ozkan/Cockpit-Keyboard/images/CockpitKeyboard.jpg

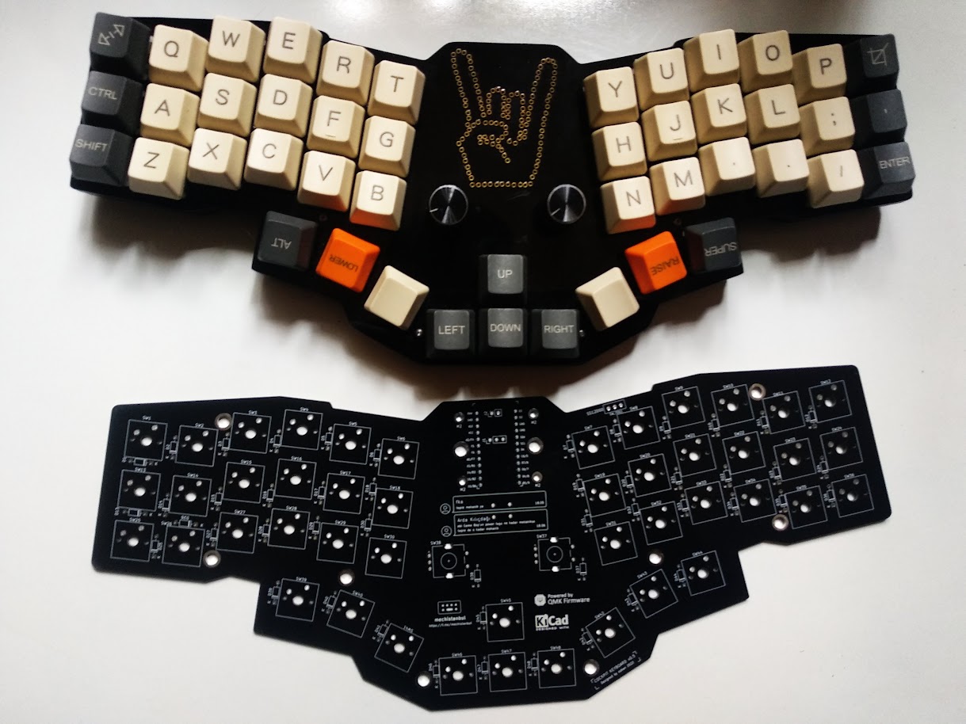
images/CockpitKeyboard.jpg
