ozkan/Cockpit-Keyboard/cockpit_hotswap/pcb/Cockpit.kicad_sch

## KiCad design cockpit_hotswap/pcb/Cockpit.kicad_sch (2024-03-19)

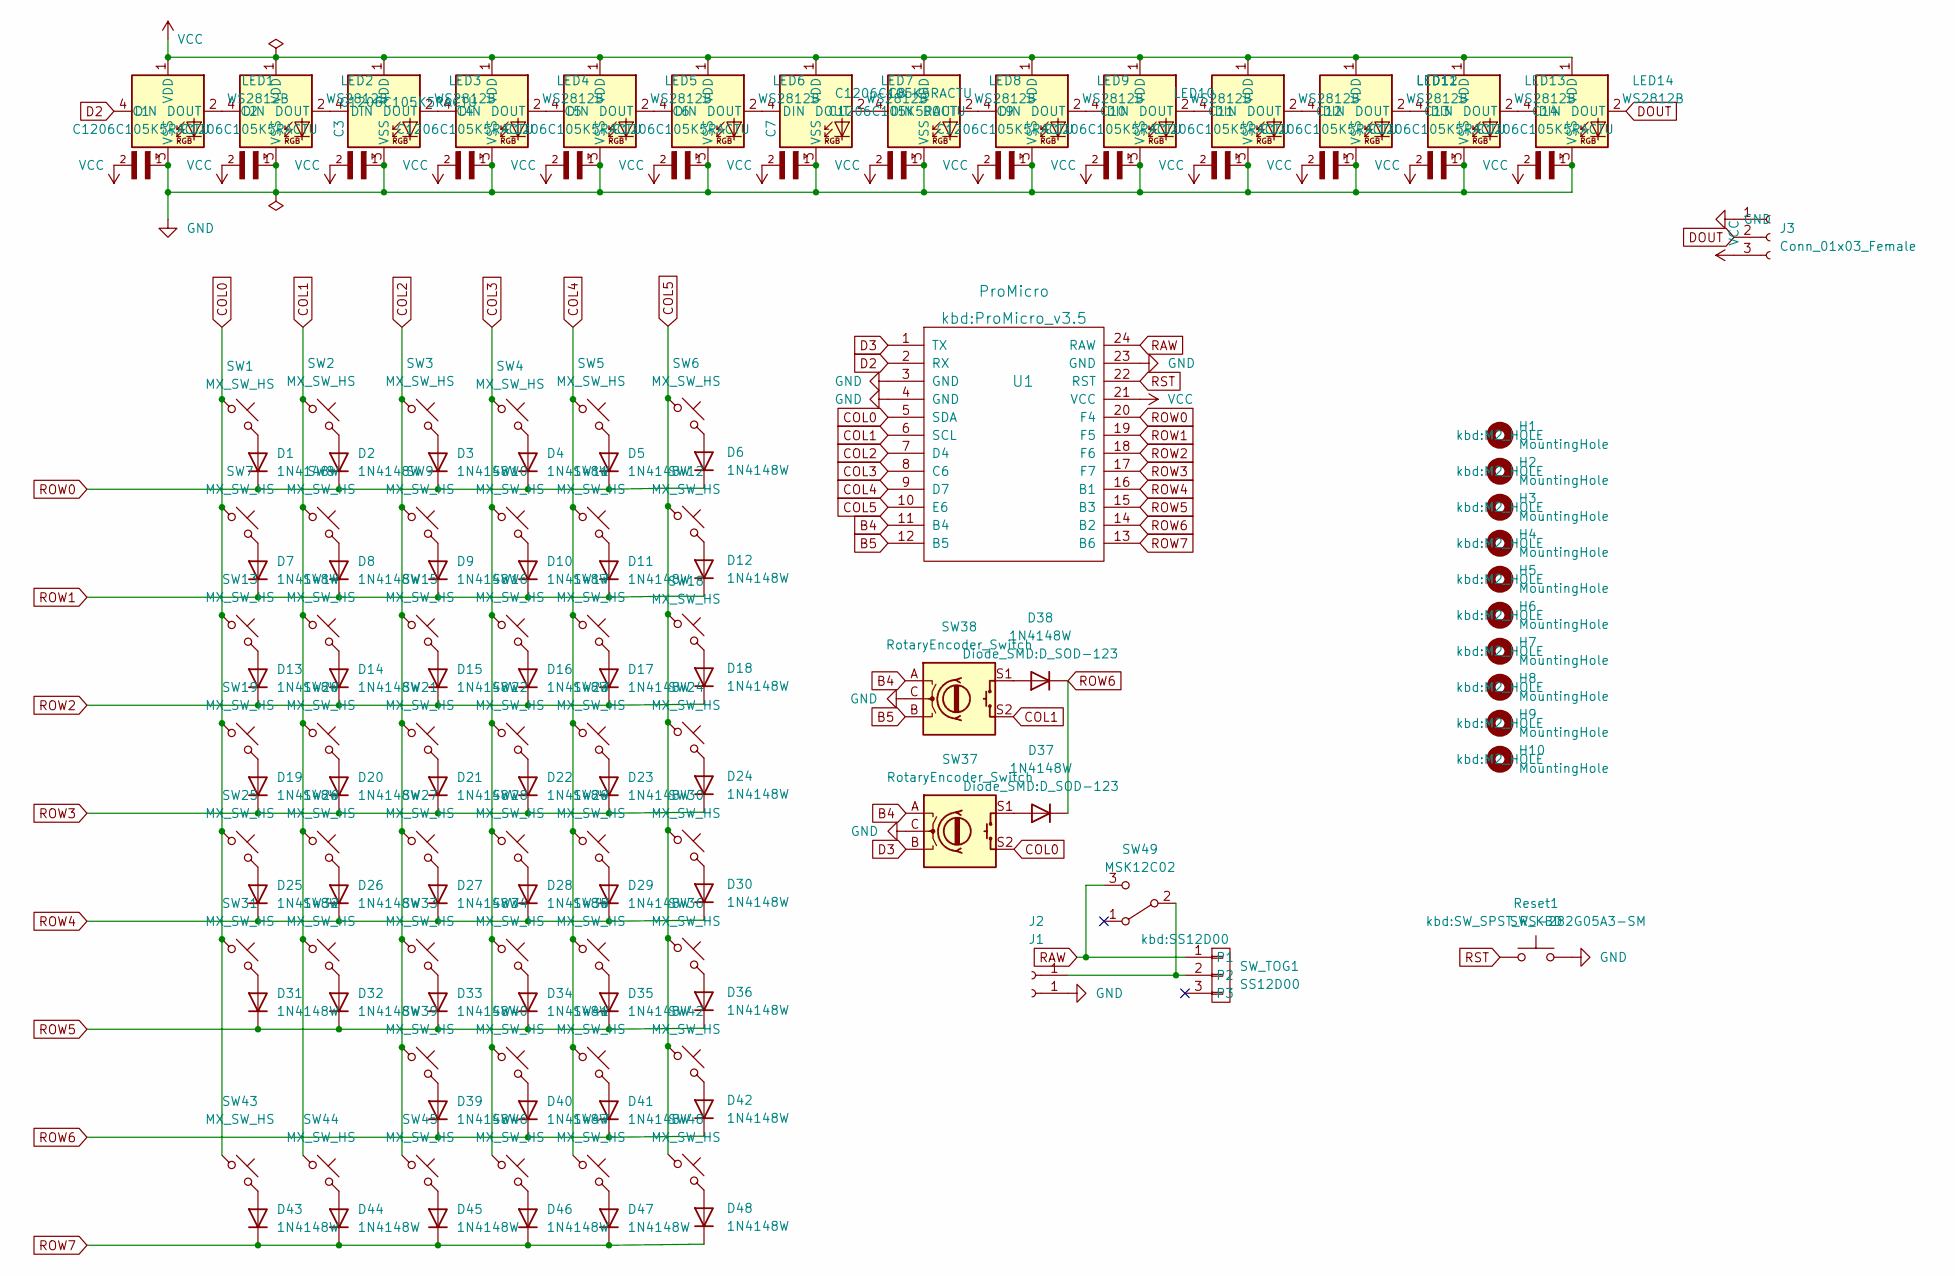
[picture p51: schematic Cockpit.kicad_sch]

Parts:
C1, C2, C3, C4, C5, C6, C7, C8, C9, C10, C11, C12, C13, C14: C1206C105K5RACTU; C_1206_3216Metric_Pad1.33x1.80mm_HandSolder
D1, D2, D3, D4, D5, D6, D7, D8, D9, D10, D11, D12, D13, D14, D15, D16, D17, D18, D19, D20, D21, D22, D23, D24, D25, D26, D27, D28, D29, D30, D31, D32, D33, D34, D35, D36, D37, D38, D39, D40, D41, D42, D43, D44, D45, D46, D47, D48: 1N4148W; D_SOD-123
H1, H2, H3, H4, H5, H6, H7, H8, H9, H10: MountingHole; M2_HOLE
J1, J2: Conn_01x01_Female; Pin_D0.9mm_L10.0mm_W2.4mm_FlatFork
J3: Conn_01x03_Female; PinHeader_1x03_P2.00mm_Vertical
LED1, LED2, LED3, LED4, LED5, LED6, LED7, LED8, LED9, LED10, LED11, LED12, LED13, LED14: WS2812B; LED_WS2812B_PLCC4_5.0x5.0mm_P3.2mm
Reset1: SW_KBD; SW_SPST_RS-282G05A3-SM
SW1, SW2, SW3, SW4, SW5, SW6, SW7, SW8, SW9, SW10, SW11, SW12, SW13, SW14, SW15, SW16, SW17, SW18, SW19, SW20, SW21, SW22, SW23, SW24, SW25, SW26, SW27, SW28, SW29, SW30, SW31, SW32, SW33, SW34, SW35, SW36, SW39, SW40, SW43, SW44, SW45, SW46, SW47, SW48: MX_SW_HS; SW_Hotswap_Kailh_MX_1.00u
SW37, SW38: RotaryEncoder_Switch; RotaryEncoder_Alps_EC11E-Switch_Vertical_H20mm
SW41, SW42: MX_SW_HS; SW_Hotswap_Kailh_MX_1.50u_90deg
SW49: MSK12C02
SW_TOG1: SS12D00
U1: ProMicro; ProMicro_v3.5

Connections:
B4: SW37.A, SW38.A, U1.11 (B4)
B5: SW38.B, U1.12 (B5)
COL0: SW1.1, SW7.1, SW13.1, SW19.1, SW25.1, SW31.1, SW37.S2, SW43.1, U1.5 (SDA)
COL1: SW2.1, SW8.1, SW14.1, SW20.1, SW26.1, SW32.1, SW38.S2, SW44.1, U1.6 (SCL)
COL2: SW3.1, SW9.1, SW15.1, SW21.1, SW27.1, SW33.1, SW39.1, SW45.1, U1.7 (D4)
COL3: SW4.1, SW10.1, SW16.1, SW22.1, SW28.1, SW34.1, SW40.1, SW46.1, U1.8 (C6)
COL4: SW5.1, SW11.1, SW17.1, SW23.1, SW29.1, SW35.1, SW41.1, SW47.1, U1.9 (D7)
COL5: SW6.1, SW12.1, SW18.1, SW24.1, SW30.1, SW36.1, SW42.1, SW48.1, U1.10 (E6)
D2: LED1.4 (DIN), U1.2 (RX)
D3: SW37.B, U1.1 (TX)
DOUT: J3.2, LED14.2 (DOUT)
GND: C1.1, C2.1, C3.1, C4.1, C5.1, C6.1, C7.1, C8.1, C9.1, C10.1, C11.1, C12.1, C13.1, C14.1, J1.1, J3.1, LED1.3 (VSS), LED2.3 (VSS), LED3.3 (VSS), LED4.3 (VSS), LED5.3 (VSS), LED6.3 (VSS), LED7.3 (VSS), LED8.3 (VSS), LED9.3 (VSS), LED10.3 (VSS), LED11.3 (VSS), LED12.3 (VSS), LED13.3 (VSS), LED14.3 (VSS), Reset1.2, SW37.C, SW38.C, U1.3 (GND), U1.4 (GND), U1.23 (GND)
unnamed: D1.2 (A), SW1.2
unnamed: D2.2 (A), SW2.2
unnamed: D3.2 (A), SW3.2
unnamed: D4.2 (A), SW4.2
unnamed: D5.2 (A), SW5.2
unnamed: D6.2 (A), SW6.2
unnamed: D7.2 (A), SW7.2
unnamed: D8.2 (A), SW8.2
unnamed: D9.2 (A), SW9.2
unnamed: D10.2 (A), SW10.2
unnamed: D11.2 (A), SW11.2
unnamed: D12.2 (A), SW12.2
unnamed: D13.2 (A), SW13.2
unnamed: D14.2 (A), SW14.2
unnamed: D15.2 (A), SW15.2
unnamed: D16.2 (A), SW16.2
unnamed: D17.2 (A), SW17.2
unnamed: D18.2 (A), SW18.2
unnamed: D19.2 (A), SW19.2
unnamed: D20.2 (A), SW20.2
unnamed: D21.2 (A), SW21.2
unnamed: D22.2 (A), SW22.2
unnamed: D23.2 (A), SW23.2
unnamed: D24.2 (A), SW24.2
unnamed: D25.2 (A), SW25.2
unnamed: D26.2 (A), SW26.2
unnamed: D27.2 (A), SW27.2
unnamed: D28.2 (A), SW28.2
unnamed: D29.2 (A), SW29.2
unnamed: D30.2 (A), SW30.2
unnamed: D31.2 (A), SW31.2
unnamed: D32.2 (A), SW32.2
unnamed: D33.2 (A), SW33.2
unnamed: D34.2 (A), SW34.2
unnamed: D35.2 (A), SW35.2
unnamed: D36.2 (A), SW36.2
unnamed: D37.2 (A), SW37.S1
unnamed: D38.2 (A), SW38.S1
unnamed: D39.2 (A), SW39.2
unnamed: D40.2 (A), SW40.2
unnamed: D41.2 (A), SW41.2
unnamed: D42.2 (A), SW42.2
unnamed: D43.2 (A), SW43.2
unnamed: D44.2 (A), SW44.2
unnamed: D45.2 (A), SW45.2
unnamed: D46.2 (A), SW46.2
unnamed: D47.2 (A), SW47.2
unnamed: D48.2 (A), SW48.2
unnamed: J2.1, SW49.2 (B), SW_TOG1.2
unnamed: LED1.2 (DOUT), LED2.4 (DIN)
unnamed: LED2.2 (DOUT), LED3.4 (DIN)
unnamed: LED3.2 (DOUT), LED4.4 (DIN)
unnamed: LED4.2 (DOUT), LED5.4 (DIN)
unnamed: LED5.2 (DOUT), LED6.4 (DIN)
unnamed: LED6.2 (DOUT), LED7.4 (DIN)
unnamed: LED7.2 (DOUT), LED8.4 (DIN)
unnamed: LED8.2 (DOUT), LED9.4 (DIN)
unnamed: LED10.2 (DOUT), LED11.4 (DIN)
unnamed: LED9.2 (DOUT), LED10.4 (DIN)
unnamed: LED11.2 (DOUT), LED12.4 (DIN)
unnamed: LED12.2 (DOUT), LED13.4 (DIN)
unnamed: LED13.2 (DOUT), LED14.4 (DIN)
RAW: SW49.3 (C), SW_TOG1.1, U1.24 (RAW)
ROW0: D1.1 (K), D2.1 (K), D3.1 (K), D4.1 (K), D5.1 (K), D6.1 (K), U1.20 (F4)
ROW1: D7.1 (K), D8.1 (K), D9.1 (K), D10.1 (K), D11.1 (K), D12.1 (K), U1.19 (F5)
ROW2: D13.1 (K), D14.1 (K), D15.1 (K), D16.1 (K), D17.1 (K), D18.1 (K), U1.18 (F6)
ROW3: D19.1 (K), D20.1 (K), D21.1 (K), D22.1 (K), D23.1 (K), D24.1 (K), U1.17 (F7)
ROW4: D25.1 (K), D26.1 (K), D27.1 (K), D28.1 (K), D29.1 (K), D30.1 (K), U1.16 (B1)
ROW5: D31.1 (K), D32.1 (K), D33.1 (K), D34.1 (K), D35.1 (K), D36.1 (K), U1.15 (B3)
ROW6: D37.1 (K), D38.1 (K), D39.1 (K), D40.1 (K), D41.1 (K), D42.1 (K), U1.14 (B2)
ROW7: D43.1 (K), D44.1 (K), D45.1 (K), D46.1 (K), D47.1 (K), D48.1 (K), U1.13 (B6)
RST: Reset1.1, U1.22 (RST)
VCC: C1.2, C2.2, C3.2, C4.2, C5.2, C6.2, C7.2, C8.2, C9.2, C10.2, C11.2, C12.2, C13.2, C14.2, J3.3, LED1.1 (VDD), LED2.1 (VDD), LED3.1 (VDD), LED4.1 (VDD), LED5.1 (VDD), LED6.1 (VDD), LED7.1 (VDD), LED8.1 (VDD), LED9.1 (VDD), LED10.1 (VDD), LED11.1 (VDD), LED12.1 (VDD), LED13.1 (VDD), LED14.1 (VDD), U1.21 (VCC)
